Tommie1236/midi-controller/model/keycaps/keycap 1u blank.FCStd

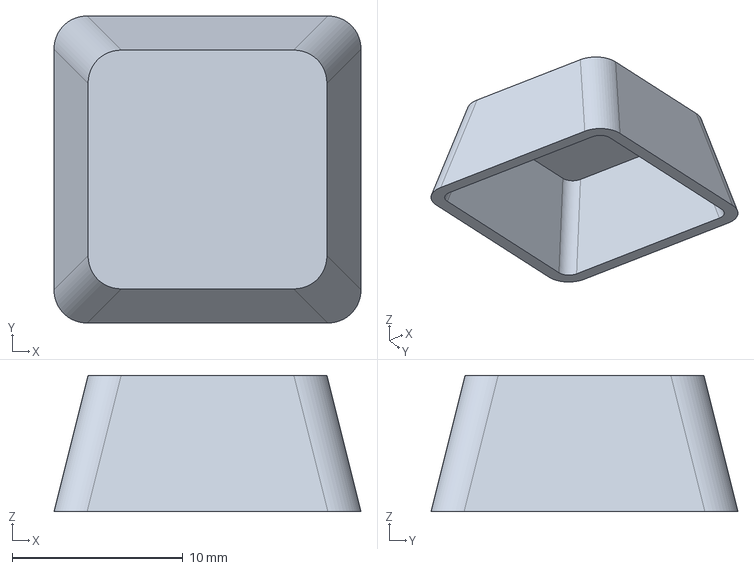
[picture p9: CAD file, 2024-09-28]
model/keycaps/keycap 1u blank.FCStd
18.0 x 18.0 x 8.00 mm
