Tommie1236/midi-controller/model/keycaps/keycap 2u blank.FCStd

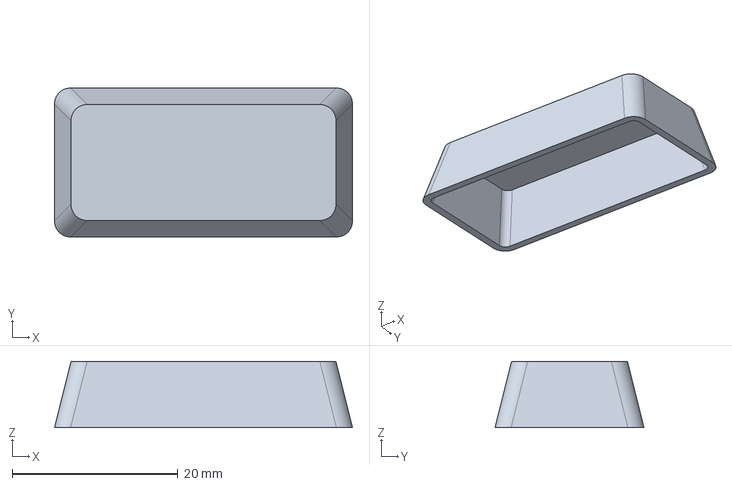
[picture p10: CAD file, 2024-09-28]
model/keycaps/keycap 2u blank.FCStd
36.0 x 18.0 x 8.00 mm
