Tommie1236/midi-controller/model/keycaps/keycap 1u B3.FCStd

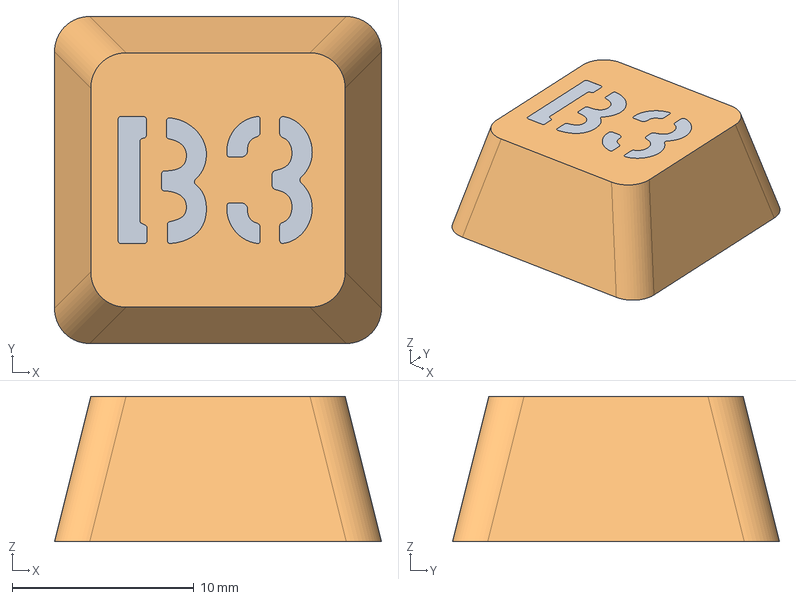
[picture p11: CAD file, 2024-09-28]
model/keycaps/keycap 1u B3.FCStd
18.0 x 18.0 x 8.00 mm
