Tommie1236/midi-controller/model/keycaps/keycap 2u insert.FCStd

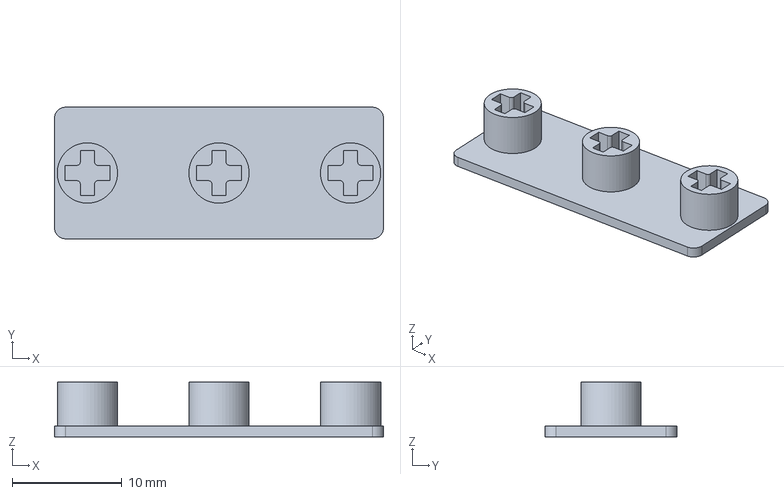
[picture p12: CAD file, 2024-09-28]
model/keycaps/keycap 2u insert.FCStd
30.0 x 12.0 x 5.00 mm
