Tommie1236/midi-controller/model/keycaps/keycap insert v1-3.stl

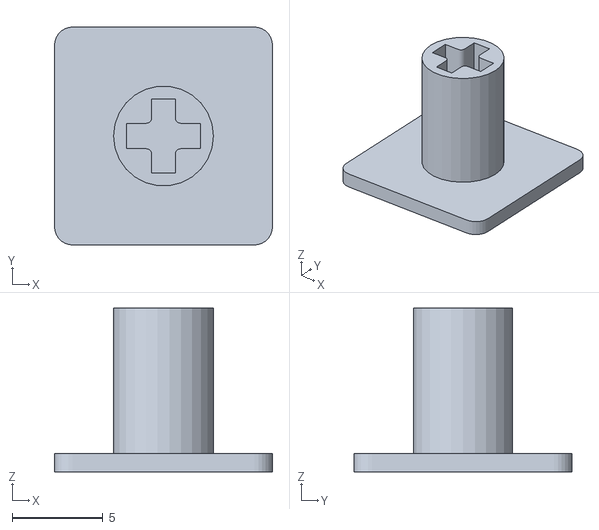
[picture p14: CAD file, 2024-09-28]
model/keycaps/keycap insert v1-3.stl
12.0 x 12.0 x 9.00
