Tommie1236/midi-controller/model/keycaps/keycap insert v1-4.stl

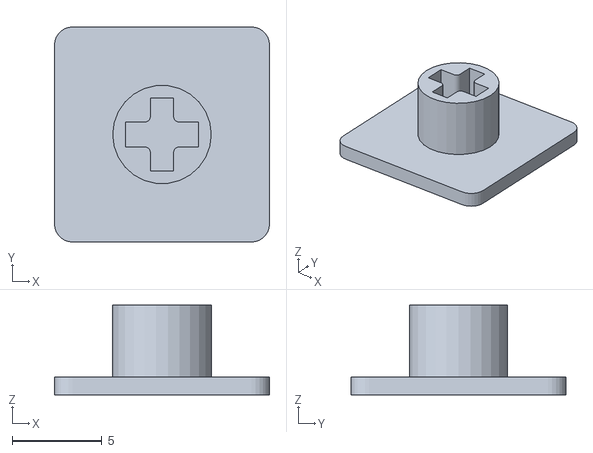
[picture p15: CAD file, 2024-09-28]
model/keycaps/keycap insert v1-4.stl
12.0 x 12.0 x 5.00
