Tommie1236/midi-controller/model/keycaps/keycap insert v1.stl

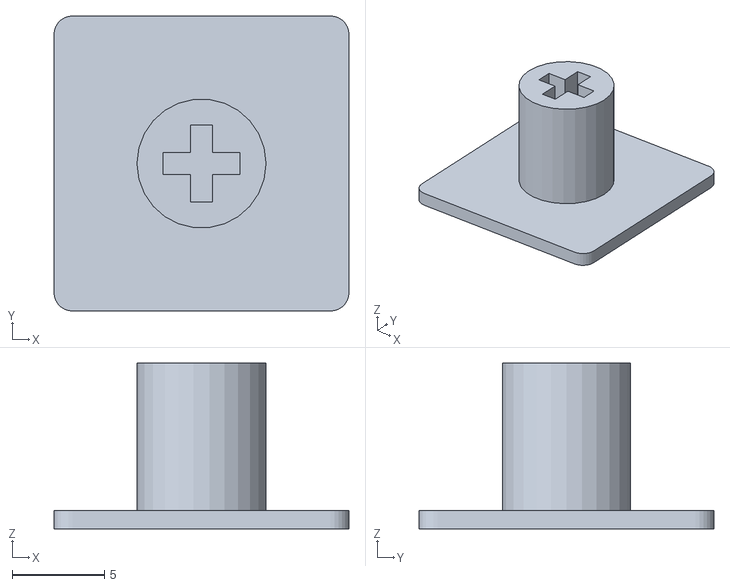
[picture p16: CAD file, 2024-08-27]
model/keycaps/keycap insert v1.stl
16.0 x 16.0 x 9.00
