Tommie1236/midi-controller/Code/src/firmware/mcp23s17/pin.cpp

#include "pin.h"
#include "mcp23s17.h"

#include "pico/stdlib.h"
#include "hardware/gpio.h"

// for rp2040 index is gpio number
// for mcp23s17 index is pin number
Pin::Pin(int index, Parent_type parent_type) : index(index), parent_type(parent_type) {};

bool Pin::set(bool value) {
    
    switch (this->parent_type) {
        case Parent_type::MCP23S17:
            
            break;
        case Parent_type::RP2040:
            gpio_put(this->index, value);
            break;
    };
    this->get();
    return this->value;
};

bool Pin::get() {
    switch (this->parent_type) {
    case Parent_type::MCP23S17:
        break;

    case Parent_type::RP2040:
        this->value = gpio_get(this->index);
        break;
    };
    return this->value;
};

void Pin::set_parent(Mcp23s17& parent) {
    this->parent = &parent;
};

bool Pin::set_default_value(bool value) {
    this->default_value = value;
    return this->default_value;
};

Interrupt_mode Pin::get_interrupt_mode() {
    return this->interrupt_mode;
};

Interrupt_mode Pin::set_interrupt_mode(Interrupt_mode interrupt_mode) {
    this->interrupt_mode = interrupt_mode;
    // TODO: implement interrupt mode
    return this->interrupt_mode;
};
